galagen8/P5-Clock-GPS/Code and fonts/InterExtraBold_50.h

/*
 *
 * InterExtraBold50
 *
 * created with FontCreator
 * written by F. Maximilian Thiele
 *
 * http://www.apetech.de/fontCreator
 * me@apetech.de
 *
 * File Name           : InterExtraBold_50.h
 * Date                : 03.09.2024
 * Font size in bytes  : 13696
 * Font width          : 50
 * Font height         : 38
 * Font first char     : 48
 * Font last char      : 58
 * Font used chars     : 10
 *
 * The font data are defined as
 *
 * struct _FONT_ {
 *     uint16_t   font_Size_in_Bytes_over_all_included_Size_it_self;
 *     uint8_t    font_Width_in_Pixel_for_fixed_drawing;
 *     uint8_t    font_Height_in_Pixel_for_all_characters;
 *     unit8_t    font_First_Char;
 *     uint8_t    font_Char_Count;
 *
 *     uint8_t    font_Char_Widths[font_Last_Char - font_First_Char +1];
 *                  // for each character the separate width in pixels,
 *                  // characters < 128 have an implicit virtual right empty row
 *
 *     uint8_t    font_data[];
 *                  // bit field of all characters
 */

#include <inttypes.h>
#include <avr/pgmspace.h>

#ifndef INTEREXTRABOLD50_H
#define INTEREXTRABOLD50_H

#define INTEREXTRABOLD50_WIDTH 50
#define INTEREXTRABOLD50_HEIGHT 38

static uint8_t InterExtraBold50[] PROGMEM = {
    0x35, 0x80, // size
    0x32, // width
    0x26, // height
    0x30, // first char
    0x0A, // char count
    
    // char widths
    0x24, 0x24, 0x24, 0x24, 0x24, 0x24, 0x24, 0x24, 0x24, 0x24, 
    
    
    // font data
    0x00, 0x00, 0x00, 0x00, 0x80, 0xC0, 0xE0, 0xF0, 0xF8, 0xFC, 0xFC, 0xFE, 0xFE, 0xFE, 0x7F, 0x7F, 0x3F, 0x3F, 0x3F, 0x7F, 0x7F, 0xFE, 0xFE, 0xFE, 0xFC, 0xFC, 0xF8, 0xF0, 0xE0, 0xC0, 0x80, 0x00, 0x00, 0x00, 0x00, 0x00, 0x00, 0x00, 0xC0, 0xFC, 0xFF, 0xFF, 0xFF, 0xFF, 0xFF, 0xFF, 0xFF, 0x7F, 0x03, 0x01, 0x00, 0x00, 0x00, 0x00, 0x00, 0x00, 0x00, 0x01, 0x03, 0x7F, 0xFF, 0xFF, 0xFF, 0xFF, 0xFF, 0xFF, 0xFF, 0xFC, 0xC0, 0x00, 0x00, 0x00, 0x00, 0x00, 0xFF, 0xFF, 0xFF, 0xFF, 0xFF, 0xFF, 0xFF, 0xFF, 0xFF, 0x80, 0x00, 0x00, 0x00, 0x00, 0x00, 0x00, 0x00, 0x00, 0x00, 0x00, 0x00, 0x80, 0xFF, 0xFF, 0xFF, 0xFF, 0xFF, 0xFF, 0xFF, 0xFF, 0xFF, 0x00, 0x00, 0x00, 0x00, 0x00, 0x00, 0x0F, 0x7F, 0xFF, 0xFF, 0xFF, 0xFF, 0xFF, 0xFF, 0xFF, 0xF0, 0xE0, 0x80, 0x80, 0x00, 0x00, 0x00, 0x80, 0x80, 0xE0, 0xF0, 0xFF, 0xFF, 0xFF, 0xFF, 0xFF, 0xFF, 0xFF, 0x7F, 0x0F, 0x00, 0x00, 0x00, 0x00, 0x00, 0x00, 0x00, 0x00, 0x00, 0x00, 0x04, 0x0C, 0x1C, 0x3C, 0x3C, 0x7C, 0x7C, 0x7C, 0xFC, 0xFC, 0xFC, 0xFC, 0xFC, 0xFC, 0xFC, 0x7C, 0x7C, 0x7C, 0x3C, 0x3C, 0x1C, 0x0C, 0x04, 0x00, 0x00, 0x00, 0x00, 0x00, 0x00, 0x00, // 48
    0x00, 0x00, 0x00, 0x00, 0x00, 0x00, 0x00, 0xE0, 0xE0, 0xF0, 0xF8, 0xF8, 0xFC, 0xFE, 0xFE, 0xFF, 0xFF, 0xFF, 0xFF, 0xFF, 0xFF, 0xFF, 0xFF, 0xFF, 0xFF, 0x00, 0x00, 0x00, 0x00, 0x00, 0x00, 0x00, 0x00, 0x00, 0x00, 0x00, 0x00, 0x00, 0x00, 0x00, 0x00, 0x00, 0x00, 0x1F, 0x0F, 0x0F, 0x07, 0x03, 0x03, 0x01, 0x00, 0x00, 0xFF, 0xFF, 0xFF, 0xFF, 0xFF, 0xFF, 0xFF, 0xFF, 0xFF, 0x00, 0x00, 0x00, 0x00, 0x00, 0x00, 0x00, 0x00, 0x00, 0x00, 0x00, 0x00, 0x00, 0x00, 0x00, 0x00, 0x00, 0x00, 0x00, 0x00, 0x00, 0x00, 0x00, 0x00, 0x00, 0x00, 0x00, 0xFF, 0xFF, 0xFF, 0xFF, 0xFF, 0xFF, 0xFF, 0xFF, 0xFF, 0x00, 0x00, 0x00, 0x00, 0x00, 0x00, 0x00, 0x00, 0x00, 0x00, 0x00, 0x00, 0x00, 0x00, 0x00, 0x00, 0x00, 0x00, 0x00, 0x00, 0x00, 0x00, 0x00, 0x00, 0x00, 0x00, 0x00, 0xFF, 0xFF, 0xFF, 0xFF, 0xFF, 0xFF, 0xFF, 0xFF, 0xFF, 0x00, 0x00, 0x00, 0x00, 0x00, 0x00, 0x00, 0x00, 0x00, 0x00, 0x00, 0x00, 0x00, 0x00, 0x00, 0x00, 0x00, 0x00, 0x00, 0x00, 0x00, 0x00, 0x00, 0x00, 0x00, 0x00, 0x00, 0xFC, 0xFC, 0xFC, 0xFC, 0xFC, 0xFC, 0xFC, 0xFC, 0xFC, 0x00, 0x00, 0x00, 0x00, 0x00, 0x00, 0x00, 0x00, 0x00, 0x00, 0x00, // 49
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
    
};

#endif
