galagen8/P5-Clock-GPS/Code and fonts/InterExtraBold_19.h

/*
 *
 * InterExtraBold19
 *
 * created with FontCreator
 * written by F. Maximilian Thiele
 *
 * http://www.apetech.de/fontCreator
 * me@apetech.de
 *
 * File Name           : InterExtraBold_19.h
 * Date                : 03.09.2024
 * Font size in bytes  : 3513
 * Font width          : 26
 * Font height         : 19
 * Font first char     : 48
 * Font last char      : 59
 * Font used chars     : 11
 *
 * The font data are defined as
 *
 * struct _FONT_ {
 *     uint16_t   font_Size_in_Bytes_over_all_included_Size_it_self;
 *     uint8_t    font_Width_in_Pixel_for_fixed_drawing;
 *     uint8_t    font_Height_in_Pixel_for_all_characters;
 *     unit8_t    font_First_Char;
 *     uint8_t    font_Char_Count;
 *
 *     uint8_t    font_Char_Widths[font_Last_Char - font_First_Char +1];
 *                  // for each character the separate width in pixels,
 *                  // characters < 128 have an implicit virtual right empty row
 *
 *     uint8_t    font_data[];
 *                  // bit field of all characters
 */

#include <inttypes.h>
#include <avr/pgmspace.h>

#ifndef INTEREXTRABOLD19_H
#define INTEREXTRABOLD19_H

#define INTEREXTRABOLD19_WIDTH 26
#define INTEREXTRABOLD19_HEIGHT 19

static uint8_t InterExtraBold19[] PROGMEM = {
    0x0D, 0xB9, // size
    0x1A, // width
    0x13, // height
    0x30, // first char
    0x0B, // char count
    
    // char widths
    0x12, 0x12, 0x12, 0x12, 0x12, 0x12, 0x12, 0x12, 0x12, 0x12, 
    0x04, 
    
    // font data
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
    0xE0, 0xE0, 0xE0, 0xE0, 0x81, 0x81, 0x81, 0x81, 0xE0, 0xE0, 0xE0, 0xE0 // 58
    
};

#endif
